gmarsh/nopesign/kicad/nopesign.kicad_sch

## KiCad design kicad/nopesign.kicad_sch (2025-06-19)

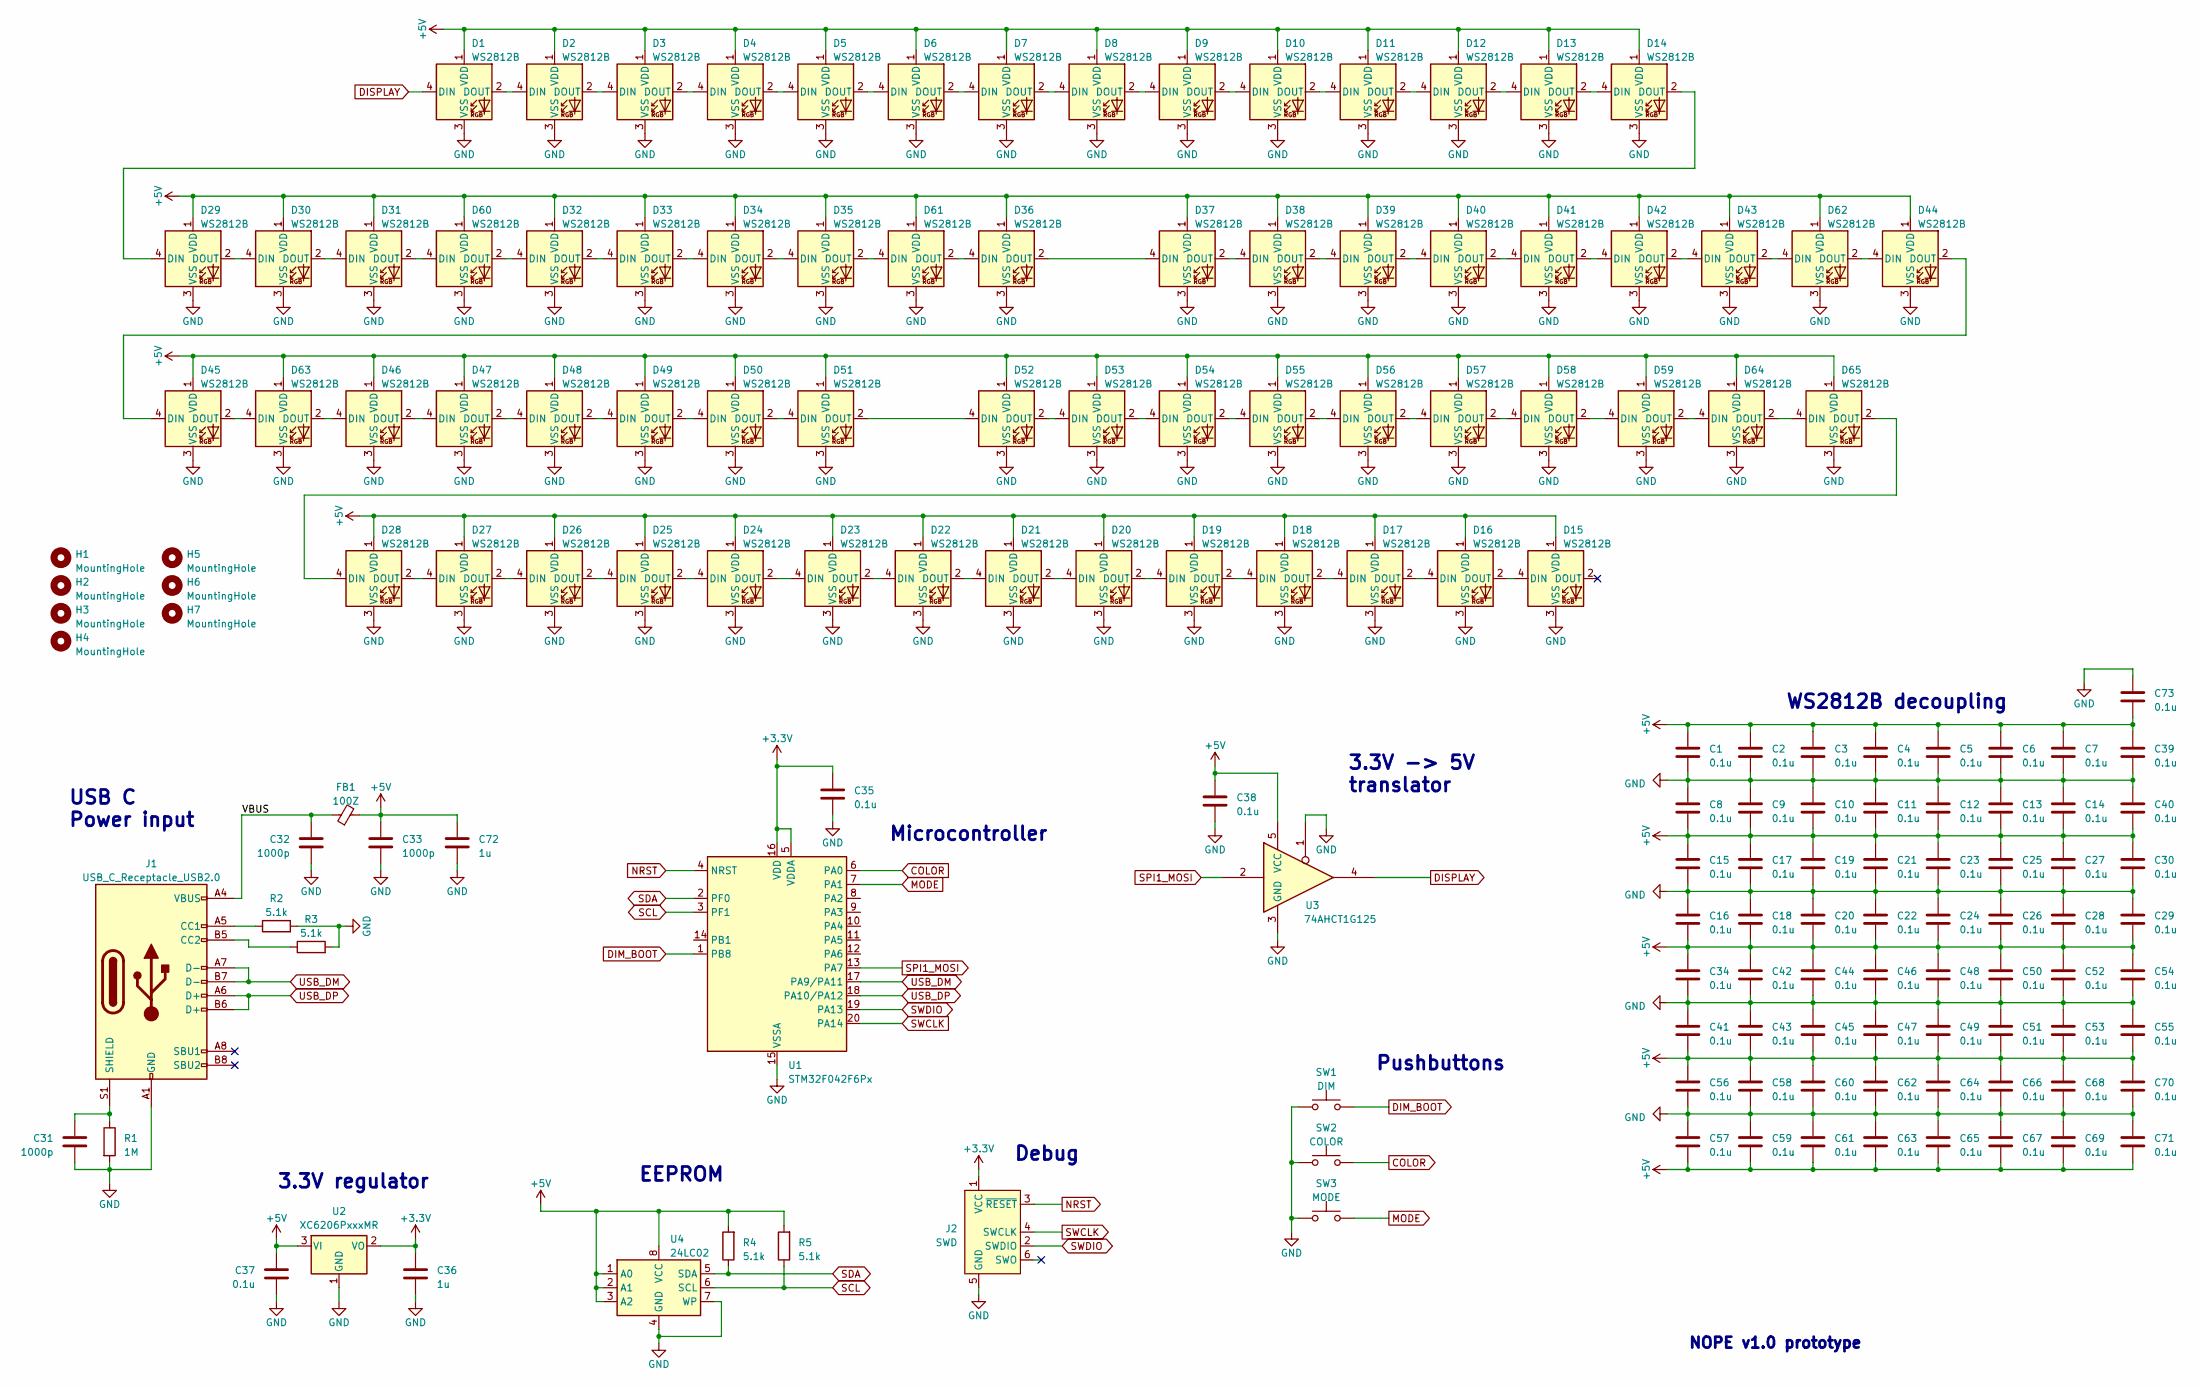
[picture p5: schematic nopesign.kicad_sch]

Parts:
C1: 0.1u; C_0603_1608Metric; LCSC C14663
C2, C3, C4, C5, C6, C7, C8, C9, C10, C11, C12, C13, C14, C15, C16, C17, C18, C19, C20, C21, C22, C23, C24, C25, C26, C27, C28, C29, C30, C34, C35, C37, C38, C39, C40, C41, C42, C43, C44, C45, C46, C47, C48, C49, C50, C51, C52, C53, C54, C55, C56, C57, C58, C59, C60, C61, C62, C63, C64, C65, C66, C67, C68, C69, C70, C71, C73: 0.1u; C_0603_1608Metric
C31, C32, C33: 1000p; C_0402_1005Metric
C36, C72: 1u; C_0805_2012Metric
D1, D2, D3, D4, D5, D6, D7, D8, D9, D10, D11, D12, D13, D14, D15, D16, D17, D18, D19, D20, D21, D22, D23, D24, D25, D26, D27, D28, D29, D30, D31, D32, D33, D34, D35, D36, D37, D38, D39, D40, D41, D42, D43, D44, D45, D46, D47, D48, D49, D50, D51, D52, D53, D54, D55, D56, D57, D58, D59, D60, D61, D62, D63, D64, D65: WS2812B; LED_WS2812B_PLCC4_5.0x5.0mm_P3.2mm
FB1: 100Z; L_0805_2012Metric
H1, H2, H3, H4, H5, H6, H7: MountingHole; ScrewHole
J1: USB_C_Receptacle_USB2.0; USB_C_Receptacle_HRO_TYPE-C-31-M-12
J2: SWD; Tag-Connect_TC2030-IDC-NL_2x03_P1.27mm_Vertical
R1: 1M; R_0402_1005Metric
R2, R3, R4, R5: 5.1k; R_0402_1005Metric
SW1: DIM; SW_Tactile_SPST_Angled_PTS645Vx83-2LFS
SW2: COLOR; SW_Tactile_SPST_Angled_PTS645Vx83-2LFS
SW3: MODE; SW_Tactile_SPST_Angled_PTS645Vx83-2LFS
U1: STM32F042F6Px; TSSOP-20_4.4x6.5mm_P0.65mm
U2: XC6206PxxxMR; SOT-23-3
U3: 74AHCT1G125; SOT-353_SC-70-5
U4: 24LC02; SO-8_3.9x4.9mm_P1.27mm

Connections:
+3.3V: C35.1, C36.1, J2.1 (VCC), U1.5 (VDDA), U1.16 (VDD), U2.2 (VO)
+5V: C1.1, C2.1, C3.1, C4.1, C5.1, C6.1, C7.1, C8.2, C9.2, C10.2, C11.2, C12.2, C13.2, C14.2, C15.1, C16.2, C17.1, C18.2, C19.1, C20.2, C21.1, C22.2, C23.1, C24.2, C25.1, C26.2, C27.1, C28.2, C29.2, C30.1, C33.1, C34.1, C37.1, C38.1, C39.1, C40.2, C41.2, C42.1, C43.2, C44.1, C45.2, C46.1, C47.2, C48.1, C49.2, C50.1, C51.2, C52.1, C53.2, C54.1, C55.2, C56.1, C57.2, C58.1, C59.2, C60.1, C61.2, C62.1, C63.2, C64.1, C65.2, C66.1, C67.2, C68.1, C69.2, C70.1, C71.2, C72.1, C73.2, D1.1 (VDD), D2.1 (VDD), D3.1 (VDD), D4.1 (VDD), D5.1 (VDD), D6.1 (VDD), D7.1 (VDD), D8.1 (VDD), D9.1 (VDD), D10.1 (VDD), D11.1 (VDD), D12.1 (VDD), D13.1 (VDD), D14.1 (VDD), D15.1 (VDD), D16.1 (VDD), D17.1 (VDD), D18.1 (VDD), D19.1 (VDD), D20.1 (VDD), D21.1 (VDD), D22.1 (VDD), D23.1 (VDD), D24.1 (VDD), D25.1 (VDD), D26.1 (VDD), D27.1 (VDD), D28.1 (VDD), D29.1 (VDD), D30.1 (VDD), D31.1 (VDD), D32.1 (VDD), D33.1 (VDD), D34.1 (VDD), D35.1 (VDD), D36.1 (VDD), D37.1 (VDD), D38.1 (VDD), D39.1 (VDD), D40.1 (VDD), D41.1 (VDD), D42.1 (VDD), D43.1 (VDD), D44.1 (VDD), D45.1 (VDD), D46.1 (VDD), D47.1 (VDD), D48.1 (VDD), D49.1 (VDD), D50.1 (VDD), D51.1 (VDD), D52.1 (VDD), D53.1 (VDD), D54.1 (VDD), D55.1 (VDD), D56.1 (VDD), D57.1 (VDD), D58.1 (VDD), D59.1 (VDD), D60.1 (VDD), D61.1 (VDD), D62.1 (VDD), D63.1 (VDD), D64.1 (VDD), D65.1 (VDD), FB1.2, R4.2, R5.2, U2.3 (VI), U3.5 (VCC), U4.1 (A0), U4.2 (A1), U4.3 (A2), U4.8 (VCC)
COLOR: SW2.1, U1.6 (PA0)
DIM_BOOT: SW1.1, U1.1 (PB8)
DISPLAY: D1.4 (DIN), U3.4
GND: C1.2, C2.2, C3.2, C4.2, C5.2, C6.2, C7.2, C8.1, C9.1, C10.1, C11.1, C12.1, C13.1, C14.1, C15.2, C16.1, C17.2, C18.1, C19.2, C20.1, C21.2, C22.1, C23.2, C24.1, C25.2, C26.1, C27.2, C28.1, C29.1, C30.2, C31.2, C32.2, C33.2, C34.2, C35.2, C36.2, C37.2, C38.2, C39.2, C40.1, C41.1, C42.2, C43.1, C44.2, C45.1, C46.2, C47.1, C48.2, C49.1, C50.2, C51.1, C52.2, C53.1, C54.2, C55.1, C56.2, C57.1, C58.2, C59.1, C60.2, C61.1, C62.2, C63.1, C64.2, C65.1, C66.2, C67.1, C68.2, C69.1, C70.2, C71.1, C72.2, C73.1, D1.3 (VSS), D2.3 (VSS), D3.3 (VSS), D4.3 (VSS), D5.3 (VSS), D6.3 (VSS), D7.3 (VSS), D8.3 (VSS), D9.3 (VSS), D10.3 (VSS), D11.3 (VSS), D12.3 (VSS), D13.3 (VSS), D14.3 (VSS), D15.3 (VSS), D16.3 (VSS), D17.3 (VSS), D18.3 (VSS), D19.3 (VSS), D20.3 (VSS), D21.3 (VSS), D22.3 (VSS), D23.3 (VSS), D24.3 (VSS), D25.3 (VSS), D26.3 (VSS), D27.3 (VSS), D28.3 (VSS), D29.3 (VSS), D30.3 (VSS), D31.3 (VSS), D32.3 (VSS), D33.3 (VSS), D34.3 (VSS), D35.3 (VSS), D36.3 (VSS), D37.3 (VSS), D38.3 (VSS), D39.3 (VSS), D40.3 (VSS), D41.3 (VSS), D42.3 (VSS), D43.3 (VSS), D44.3 (VSS), D45.3 (VSS), D46.3 (VSS), D47.3 (VSS), D48.3 (VSS), D49.3 (VSS), D50.3 (VSS), D51.3 (VSS), D52.3 (VSS), D53.3 (VSS), D54.3 (VSS), D55.3 (VSS), D56.3 (VSS), D57.3 (VSS), D58.3 (VSS), D59.3 (VSS), D60.3 (VSS), D61.3 (VSS), D62.3 (VSS), D63.3 (VSS), D64.3 (VSS), D65.3 (VSS), J1.A1 (GND), J1.A12 (GND), J1.B1 (GND), J1.B12 (GND), J2.5 (GND), R1.2, R2.2, R3.2, SW1.2, SW2.2, SW3.2, U1.15 (VSSA), U2.1 (GND), U3.1, U3.3 (GND), U4.4 (GND), U4.7 (WP)
MODE: SW3.1, U1.7 (PA1)
NRST: J2.3 (~RESET), U1.4 (NRST)
unnamed: C31.1, J1.S1 (SHIELD), R1.1
unnamed: D1.2 (DOUT), D2.4 (DIN)
unnamed: D2.2 (DOUT), D3.4 (DIN)
unnamed: D3.2 (DOUT), D4.4 (DIN)
unnamed: D4.2 (DOUT), D5.4 (DIN)
unnamed: D5.2 (DOUT), D6.4 (DIN)
unnamed: D6.2 (DOUT), D7.4 (DIN)
unnamed: D7.2 (DOUT), D8.4 (DIN)
unnamed: D8.2 (DOUT), D9.4 (DIN)
unnamed: D10.2 (DOUT), D11.4 (DIN)
unnamed: D9.2 (DOUT), D10.4 (DIN)
unnamed: D11.2 (DOUT), D12.4 (DIN)
unnamed: D12.2 (DOUT), D13.4 (DIN)
unnamed: D13.2 (DOUT), D14.4 (DIN)
unnamed: D14.2 (DOUT), D29.4 (DIN)
unnamed: D15.4 (DIN), D16.2 (DOUT)
unnamed: D16.4 (DIN), D17.2 (DOUT)
unnamed: D17.4 (DIN), D18.2 (DOUT)
unnamed: D18.4 (DIN), D19.2 (DOUT)
unnamed: D19.4 (DIN), D20.2 (DOUT)
unnamed: D20.4 (DIN), D21.2 (DOUT)
unnamed: D21.4 (DIN), D22.2 (DOUT)
unnamed: D22.4 (DIN), D23.2 (DOUT)
unnamed: D23.4 (DIN), D24.2 (DOUT)
unnamed: D24.4 (DIN), D25.2 (DOUT)
unnamed: D25.4 (DIN), D26.2 (DOUT)
unnamed: D26.4 (DIN), D27.2 (DOUT)
unnamed: D27.4 (DIN), D28.2 (DOUT)
unnamed: D28.4 (DIN), D65.2 (DOUT)
unnamed: D29.2 (DOUT), D30.4 (DIN)
unnamed: D30.2 (DOUT), D31.4 (DIN)
unnamed: D31.2 (DOUT), D60.4 (DIN)
unnamed: D32.2 (DOUT), D33.4 (DIN)
unnamed: D32.4 (DIN), D60.2 (DOUT)
unnamed: D33.2 (DOUT), D34.4 (DIN)
unnamed: D34.2 (DOUT), D35.4 (DIN)
unnamed: D35.2 (DOUT), D61.4 (DIN)
unnamed: D36.2 (DOUT), D37.4 (DIN)
unnamed: D36.4 (DIN), D61.2 (DOUT)
unnamed: D37.2 (DOUT), D38.4 (DIN)
unnamed: D38.2 (DOUT), D39.4 (DIN)
unnamed: D39.2 (DOUT), D40.4 (DIN)
unnamed: D40.2 (DOUT), D41.4 (DIN)
unnamed: D41.2 (DOUT), D42.4 (DIN)
unnamed: D42.2 (DOUT), D43.4 (DIN)
unnamed: D43.2 (DOUT), D62.4 (DIN)
unnamed: D44.2 (DOUT), D45.4 (DIN)
unnamed: D44.4 (DIN), D62.2 (DOUT)
unnamed: D45.2 (DOUT), D63.4 (DIN)
unnamed: D46.2 (DOUT), D47.4 (DIN)
unnamed: D46.4 (DIN), D63.2 (DOUT)
unnamed: D47.2 (DOUT), D48.4 (DIN)
unnamed: D48.2 (DOUT), D49.4 (DIN)
unnamed: D49.2 (DOUT), D50.4 (DIN)
unnamed: D50.2 (DOUT), D51.4 (DIN)
unnamed: D51.2 (DOUT), D52.4 (DIN)
unnamed: D52.2 (DOUT), D53.4 (DIN)
unnamed: D53.2 (DOUT), D54.4 (DIN)
unnamed: D54.2 (DOUT), D55.4 (DIN)
unnamed: D55.2 (DOUT), D56.4 (DIN)
unnamed: D56.2 (DOUT), D57.4 (DIN)
unnamed: D57.2 (DOUT), D58.4 (DIN)
unnamed: D58.2 (DOUT), D59.4 (DIN)
unnamed: D59.2 (DOUT), D64.4 (DIN)
unnamed: D64.2 (DOUT), D65.4 (DIN)
unnamed: J1.A5 (CC1), R2.1
unnamed: J1.B5 (CC2), R3.1
SCL: R5.1, U1.3 (PF1), U4.6 (SCL)
SDA: R4.1, U1.2 (PF0), U4.5 (SDA)
SPI1_MOSI: U1.13 (PA7), U3.2
SWCLK: J2.4 (SWCLK), U1.20 (PA14)
SWDIO: J2.2 (SWDIO), U1.19 (PA13)
USB_DM: J1.A7 (D-), J1.B7 (D-), U1.17 (PA9/PA11)
USB_DP: J1.A6 (D+), J1.B6 (D+), U1.18 (PA10/PA12)
VBUS: C32.1, FB1.1, J1.A4 (VBUS), J1.A9 (VBUS), J1.B4 (VBUS), J1.B9 (VBUS)

Notes on the sheet:
WS2812B decoupling
NOPE v1.0 prototype
3.3V regulator
Pushbuttons
3.3V -> 5V translator
USB C Power input
EEPROM
Microcontroller
Debug
